Photonenkollektiv/meterized-led-magic/images/end_long.jpeg

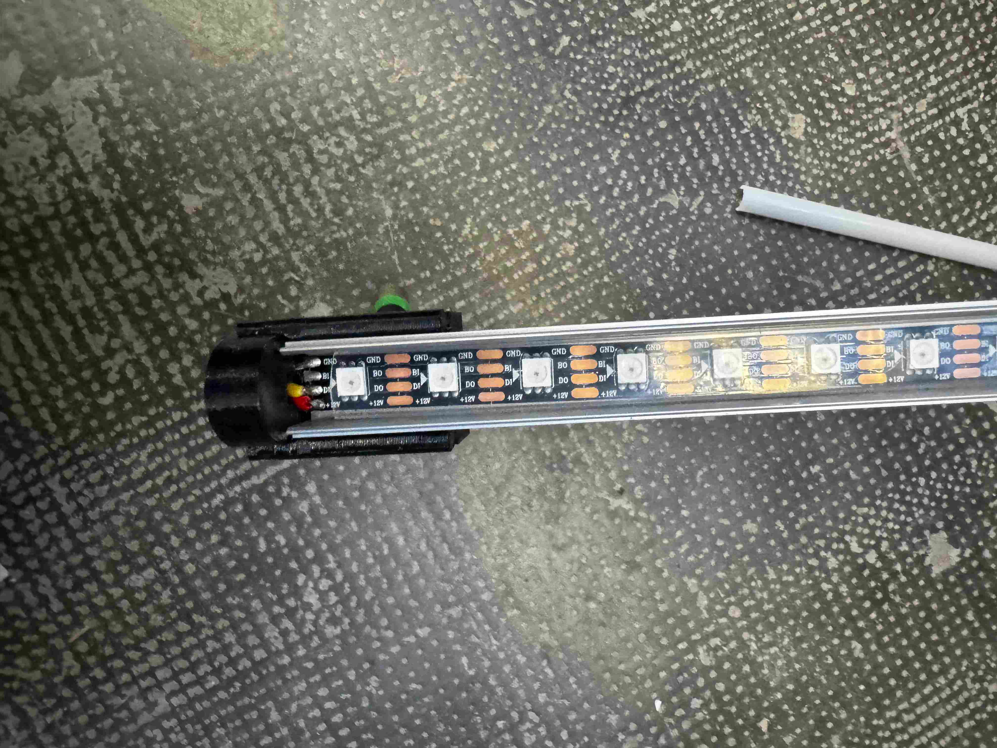
images/end_long.jpeg
