Photonenkollektiv/meterized-led-magic/images/end_with_cable.jpeg

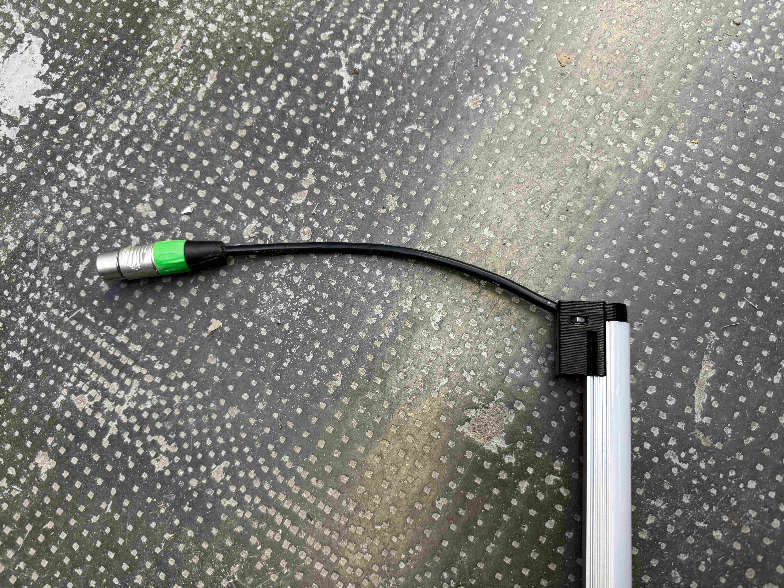
images/end_with_cable.jpeg
