Photonenkollektiv/meterized-led-magic/images/endcap_1.jpeg

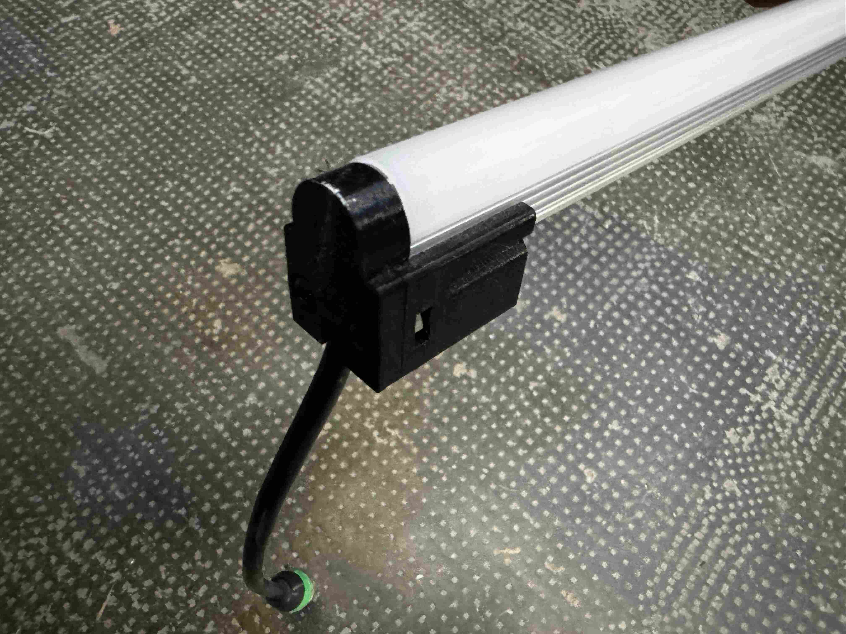
images/endcap_1.jpeg
