Photonenkollektiv/meterized-led-magic/images/endcap_2.jpeg

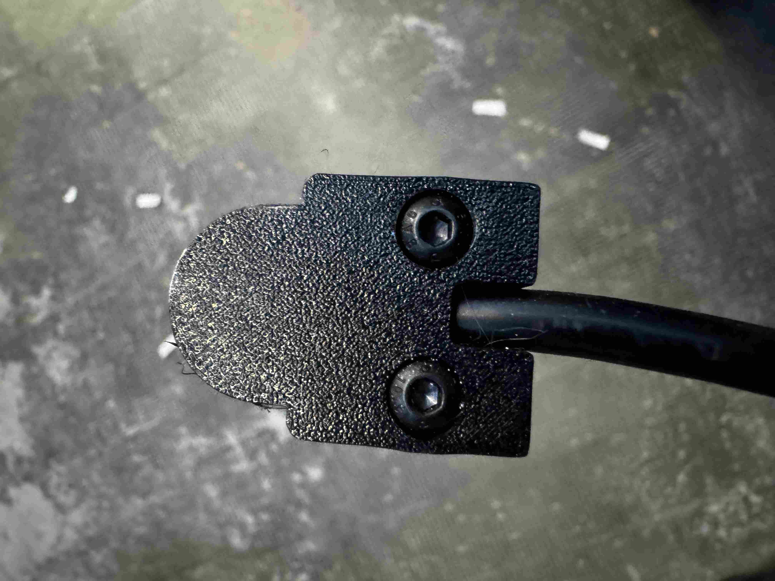
images/endcap_2.jpeg
